PrHumal/DLLL/komponendid/Karp 1.png

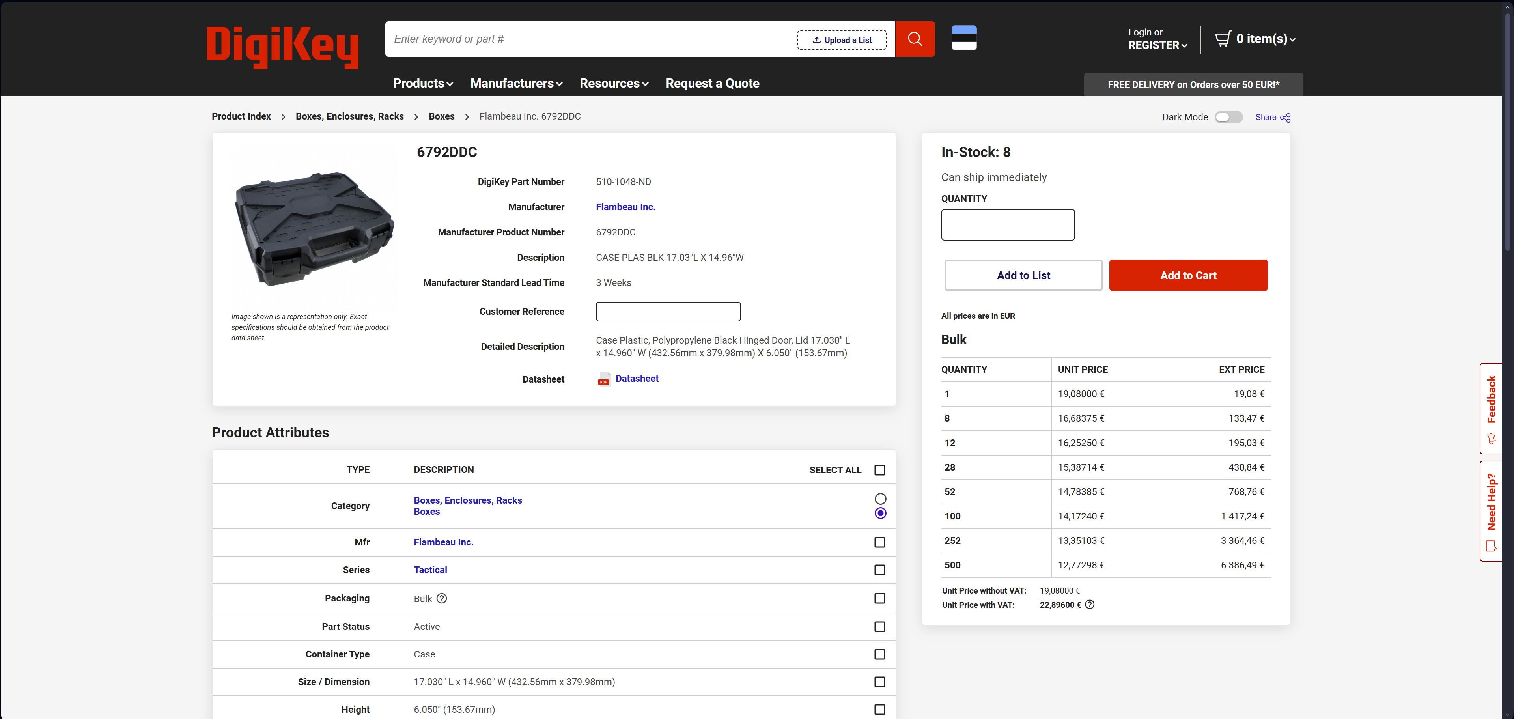
komponendid/Karp 1.png
